ojaksch/MiSTer_tty2tft/pictures/d1r32-mod-with_touch.jpg

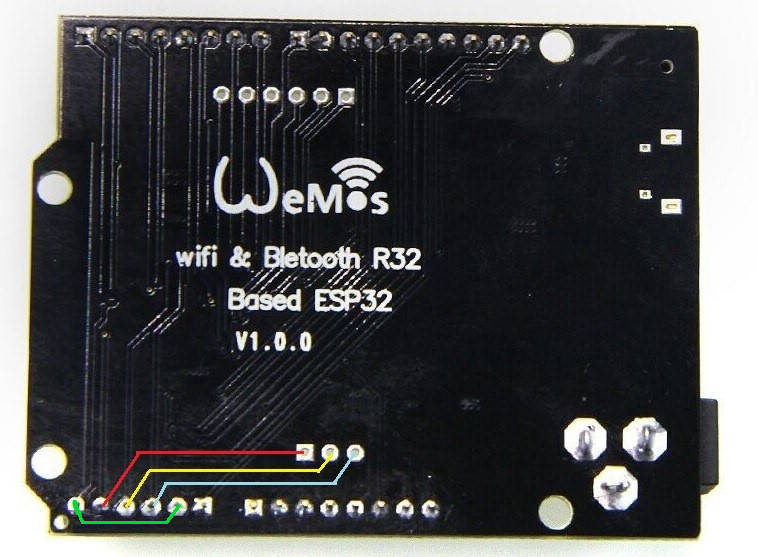
pictures/d1r32-mod-with_touch.jpg
