ojaksch/MiSTer_tty2tft/SD_card_content/jpg/320x240/#/000-nowifi.jpg

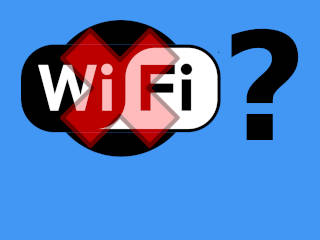
SD_card_content/jpg/320x240/#/000-nowifi.jpg
