ojaksch/MiSTer_tty2tft/SD_card_content/jpg/480x320/#/000-touchscreen.jpg

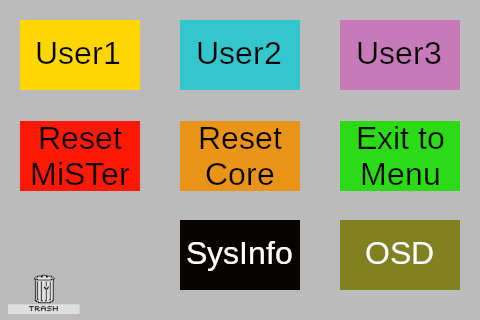
SD_card_content/jpg/480x320/#/000-touchscreen.jpg
