ojaksch/MiSTer_tty2tft/SD_card_content/mjpeg/320x240/M/MENU.jpg

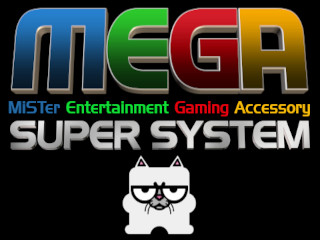
SD_card_content/mjpeg/320x240/M/MENU.jpg
