ojaksch/MiSTer_tty2tft/SD_card_content/mjpeg/480x320/M/MENU.jpg

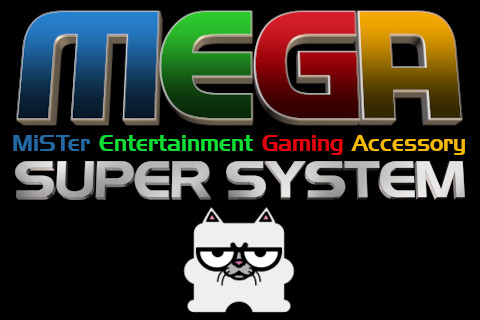
SD_card_content/mjpeg/480x320/M/MENU.jpg
